nshoemaker/LowPowerRangers/www/images/03.31.16EagleLayout.JPG

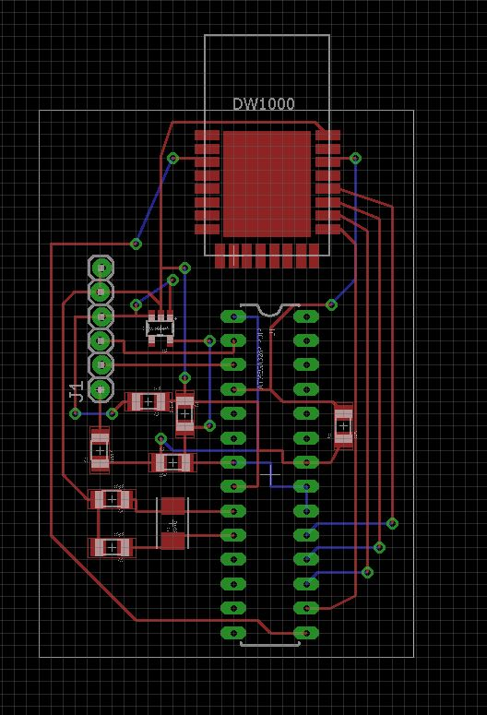
www/images/03.31.16EagleLayout.JPG
