nshoemaker/LowPowerRangers/www/images/2016.02.29.jpeg

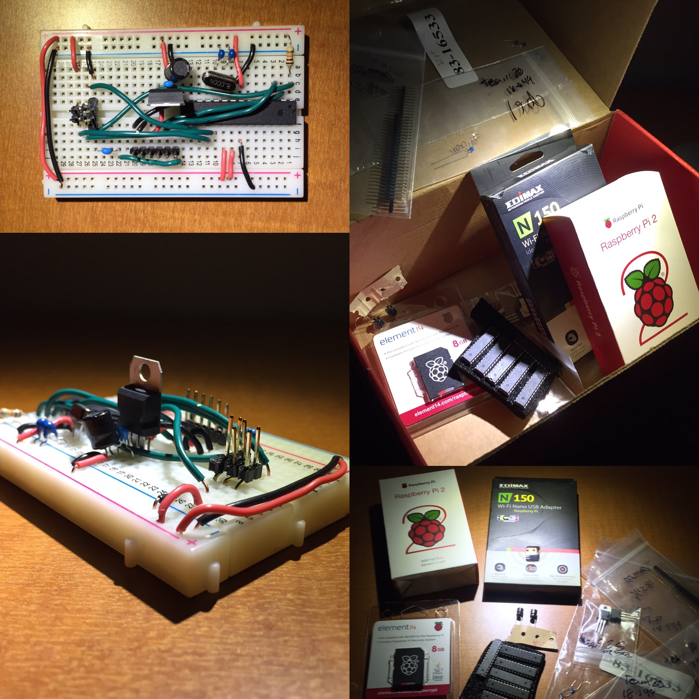
www/images/2016.02.29.jpeg
