nshoemaker/LowPowerRangers/www/images/2016.03.15.jpg

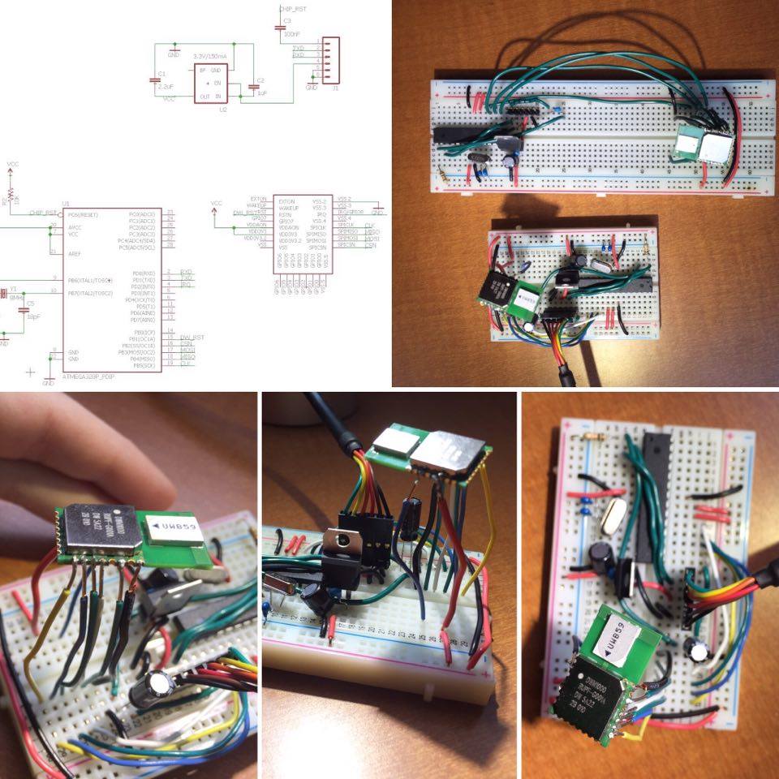
www/images/2016.03.15.jpg
