nshoemaker/LowPowerRangers/www/images/atmega.jpg

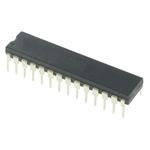
www/images/atmega.jpg
