nshoemaker/LowPowerRangers/www/images/bdsr.JPG

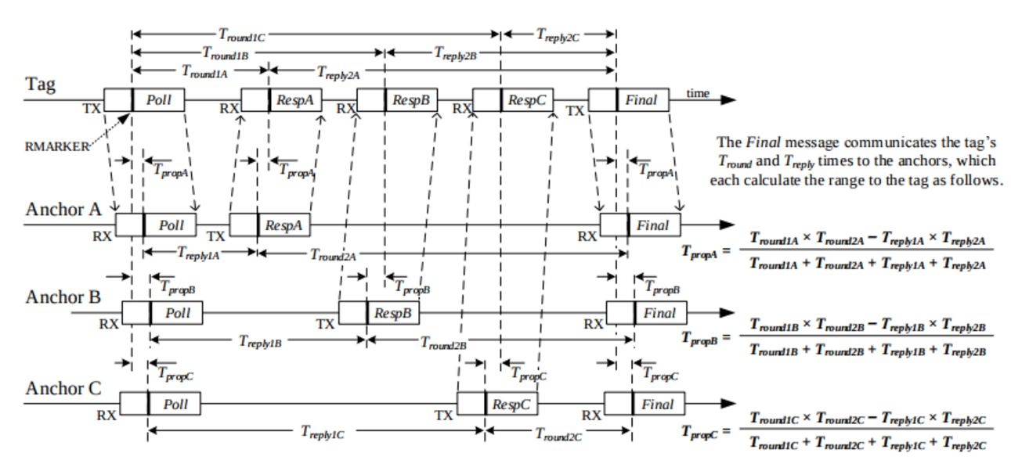
www/images/bdsr.JPG
