nshoemaker/LowPowerRangers/www/images/block1.jpeg

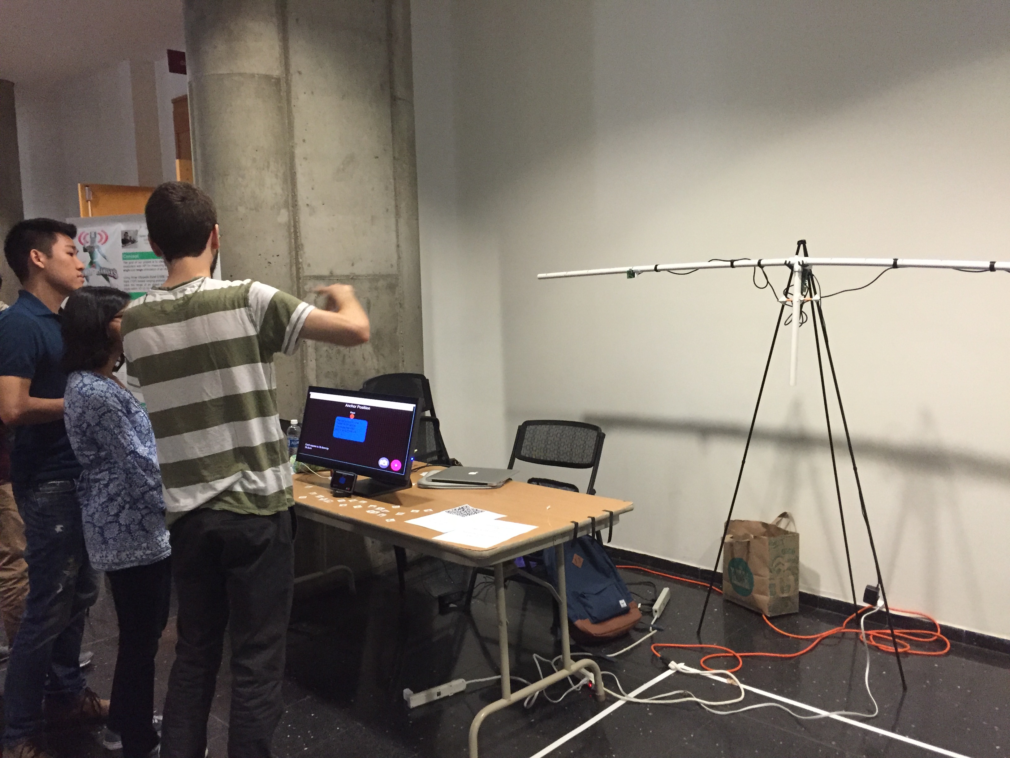
www/images/block1.jpeg
