nshoemaker/LowPowerRangers/www/images/block2.jpeg

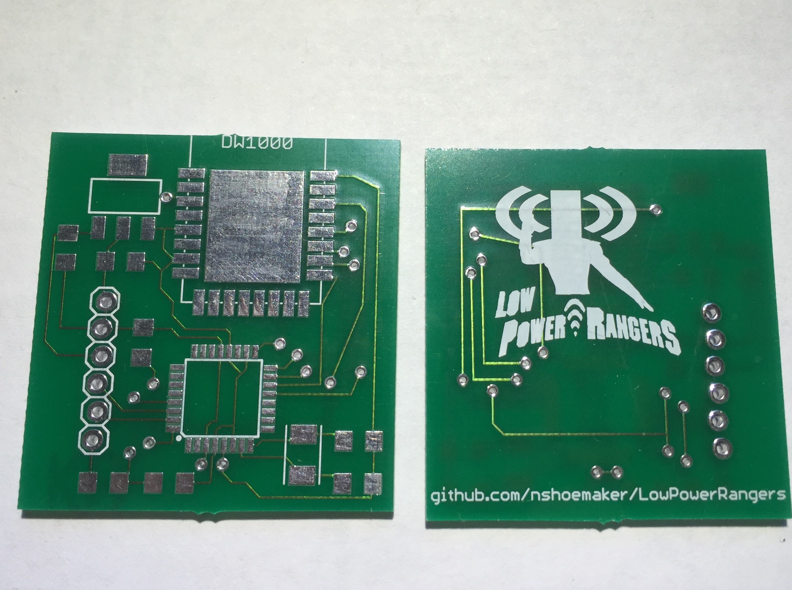
www/images/block2.jpeg
