nshoemaker/LowPowerRangers/www/images/block3.jpeg

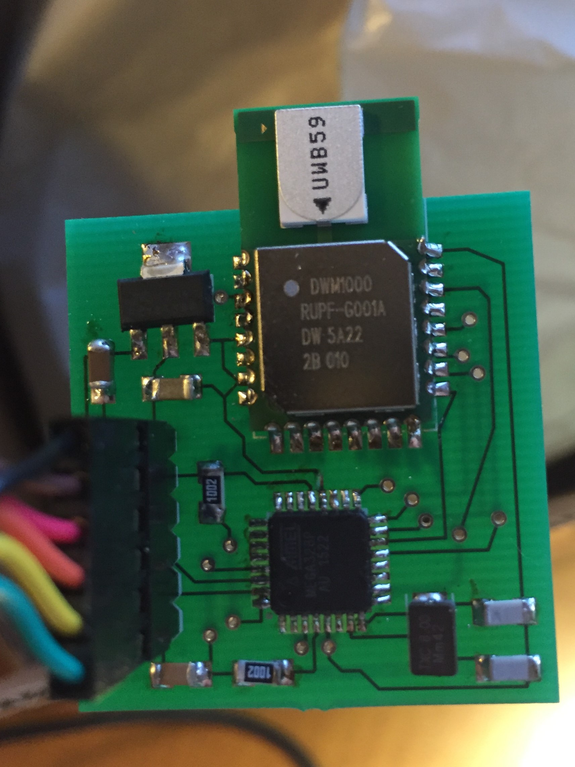
www/images/block3.jpeg
