nshoemaker/LowPowerRangers/www/images/block4.jpeg

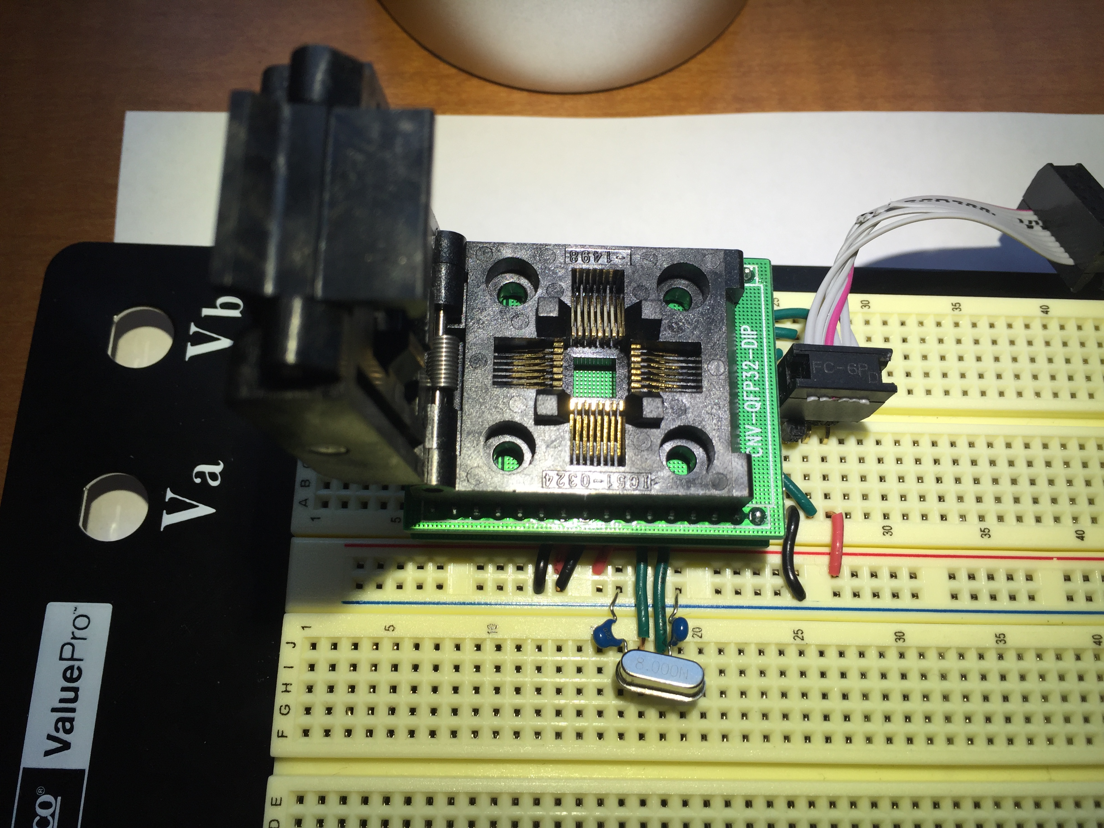
www/images/block4.jpeg
