nshoemaker/LowPowerRangers/www/images/block5.JPG

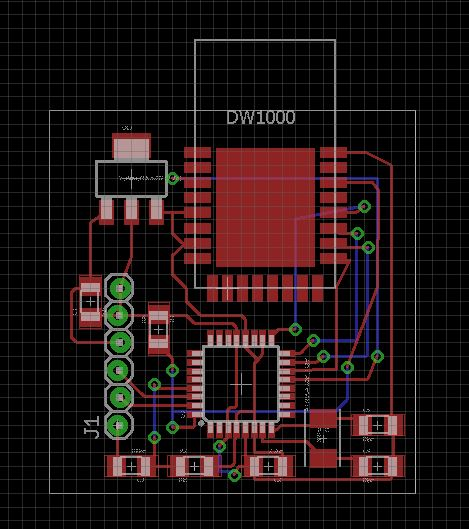
www/images/block5.JPG
