nshoemaker/LowPowerRangers/www/images/block7.jpg

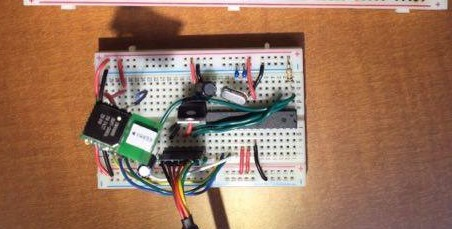
www/images/block7.jpg
