nshoemaker/LowPowerRangers/www/images/block8.jpg

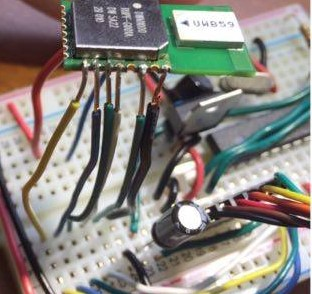
www/images/block8.jpg
