nshoemaker/LowPowerRangers/www/images/block9.jpg

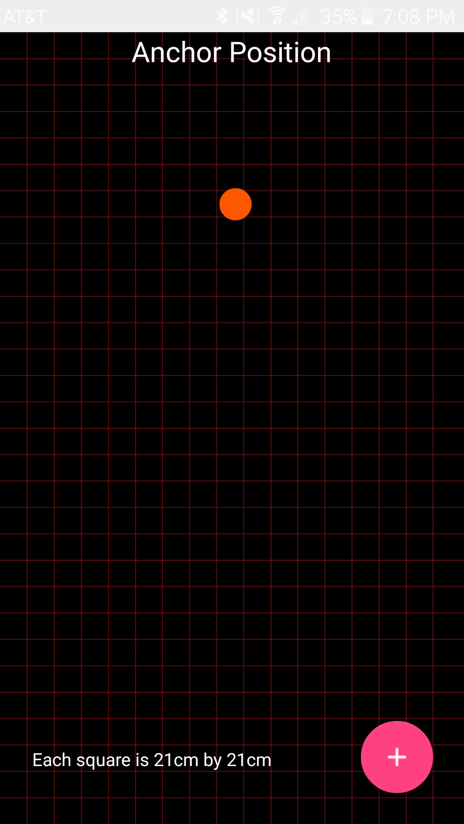
www/images/block9.jpg
