nshoemaker/LowPowerRangers/www/images/board_final.png

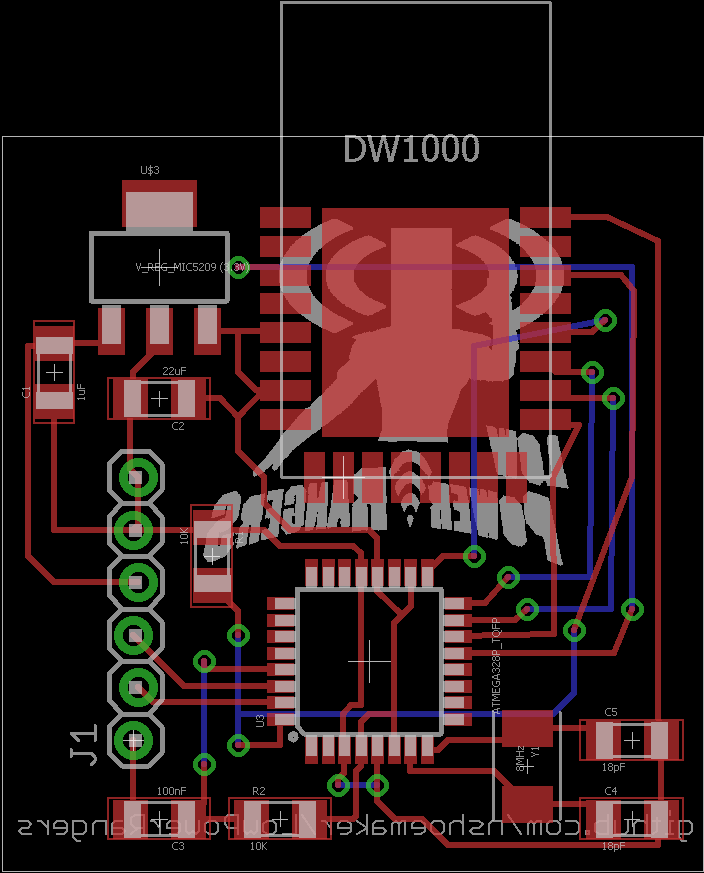
www/images/board_final.png
