nshoemaker/LowPowerRangers/www/images/decawave.jpg

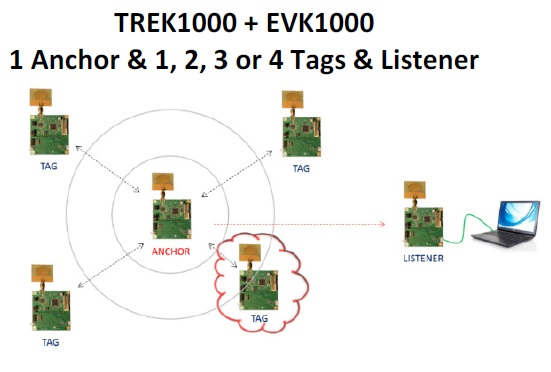
www/images/decawave.jpg
