nshoemaker/LowPowerRangers/www/images/dwm.jpg

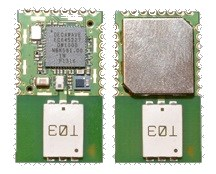
www/images/dwm.jpg
