nshoemaker/LowPowerRangers/www/images/estimote.png

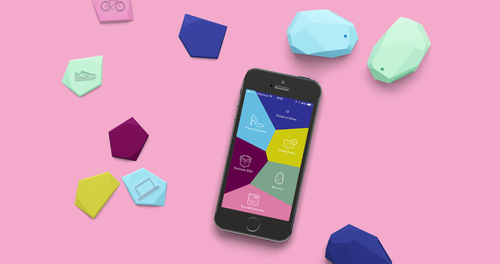
www/images/estimote.png
