nshoemaker/LowPowerRangers/www/images/RangeLargeText.png

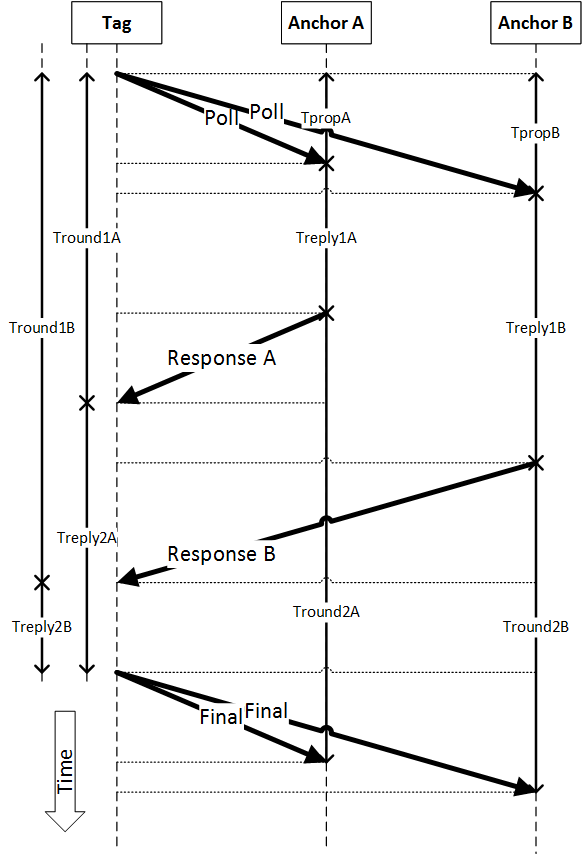
www/images/RangeLargeText.png
