nshoemaker/LowPowerRangers/www/images/redpin.png

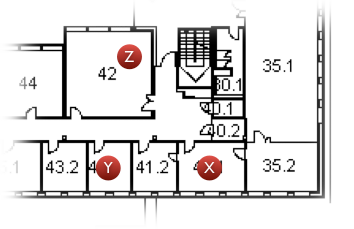
www/images/redpin.png
