nshoemaker/LowPowerRangers/www/images/spi.jpg

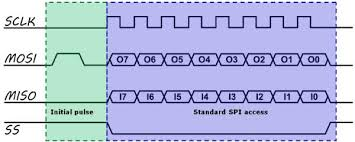
www/images/spi.jpg
