nshoemaker/LowPowerRangers/www/images/twr.JPG

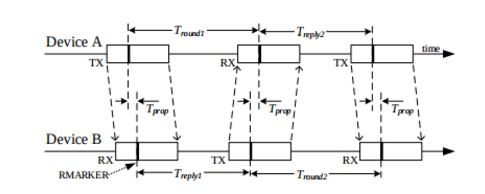
www/images/twr.JPG
