nshoemaker/LowPowerRangers/www/images/uart.jpg

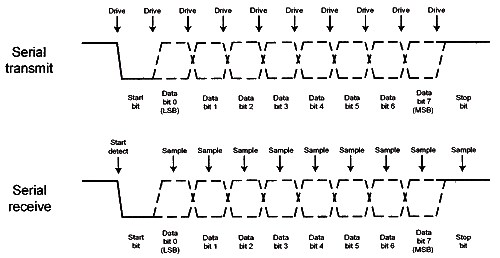
www/images/uart.jpg
