nshoemaker/LowPowerRangers/www/images/user_interaction.JPG

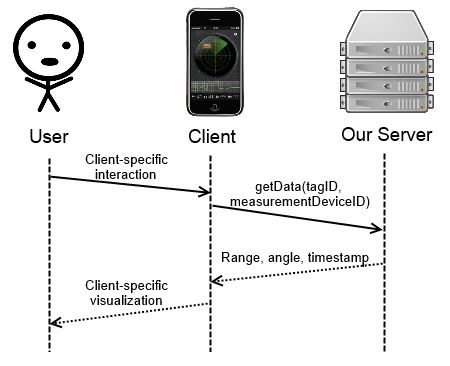
www/images/user_interaction.JPG
