nshoemaker/LowPowerRangers/www/images/wall.jpeg

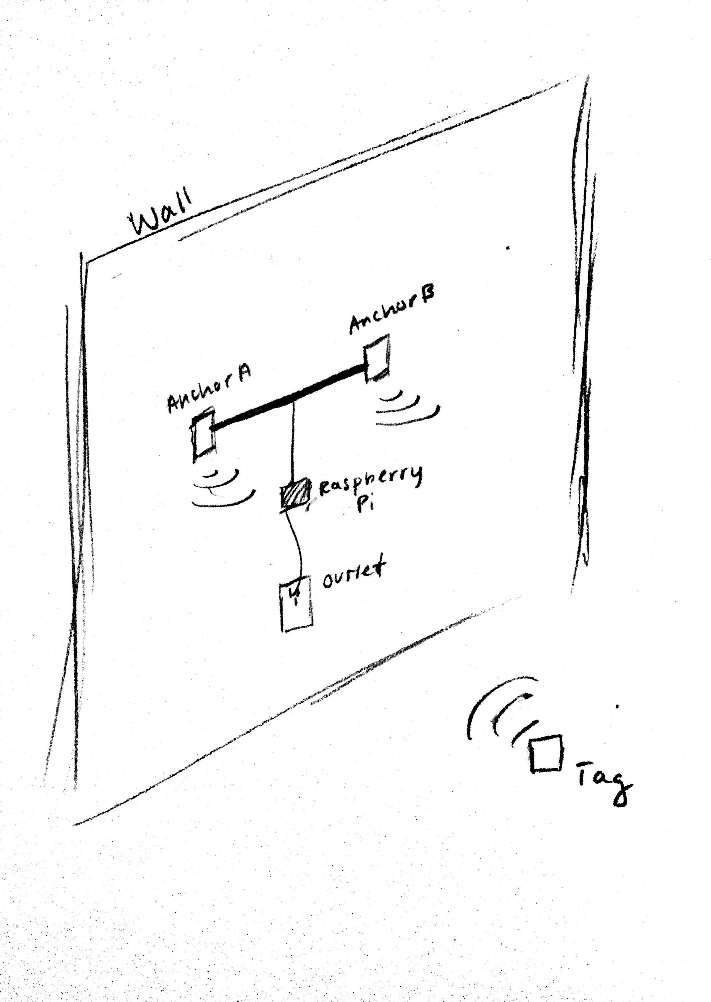
www/images/wall.jpeg
