nshoemaker/LowPowerRangers/hardware/boards/research/stolen_setup.JPG

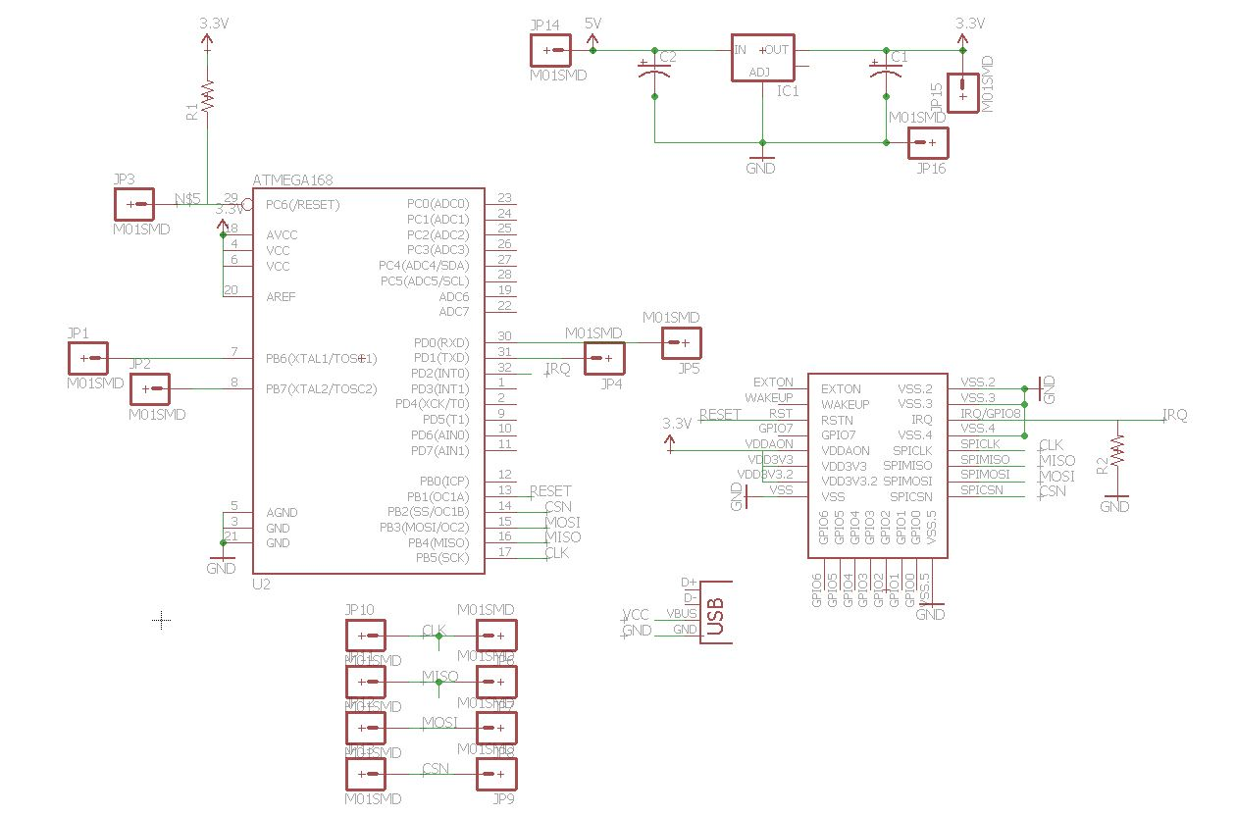
hardware/boards/research/stolen_setup.JPG
